Qtrocious/AuraCTRL/PCB/Radiant.kicad_sch

## KiCad design PCB/Radiant.kicad_sch (2025-06-26)

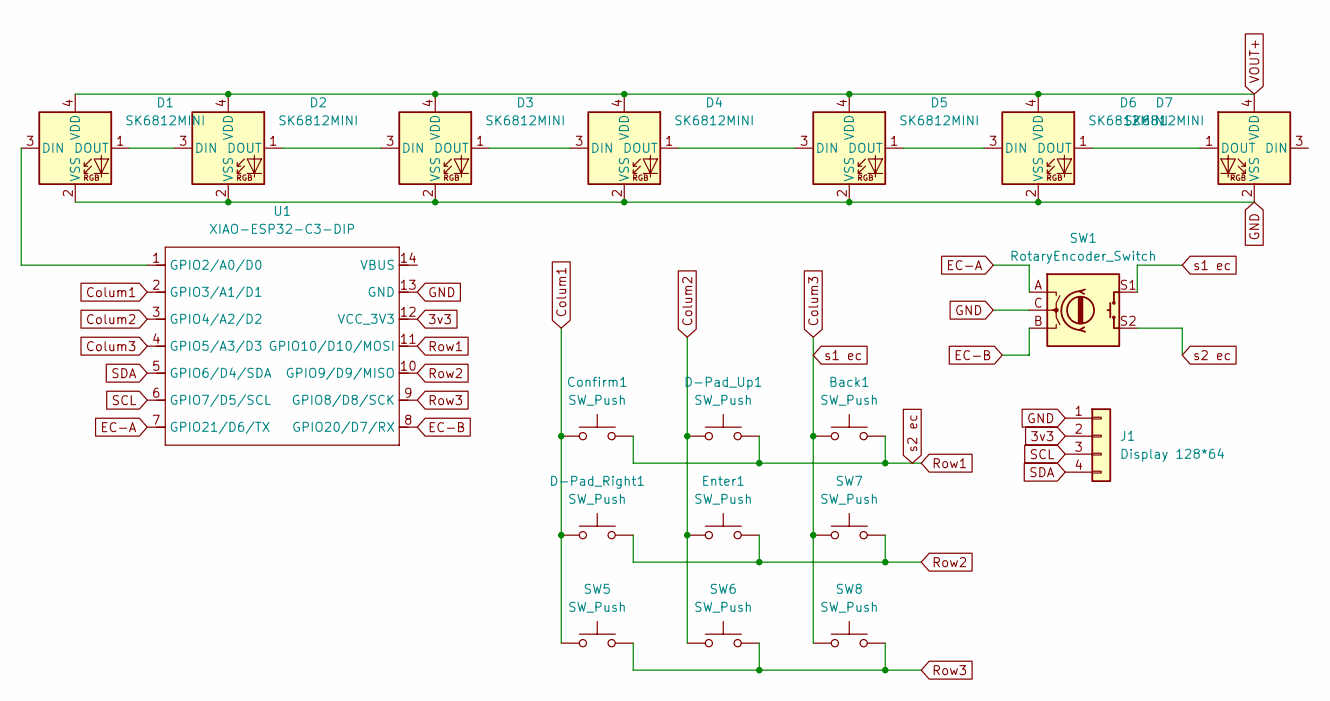
[picture p13: schematic Radiant.kicad_sch]

Parts:
Back1: SW_Push; SW_PUSH_6mm
Confirm1: SW_Push; SW_PUSH_6mm
D1, D2, D3, D4, D5, D6, D7: SK6812MINI; SK6812-MINI-E
D-Pad_Right1: SW_Push; SW_PUSH_6mm
D-Pad_Up1: SW_Push; SW_PUSH_6mm
Enter1: SW_Push; SW_PUSH_6mm
J1: Display 128*64; 128x64OLED
SW1: RotaryEncoder_Switch; RotaryEncoder_Alps_EC11E-Switch_Vertical_H20mm
SW5, SW6, SW7, SW8: SW_Push; SW_PUSH_6mm
U1: XIAO-ESP32-C3-DIP; XIAO-ESP32C3-DIP

Connections:
3v3: J1.2, U1.12 (VCC_3V3)
Colum1: Confirm1.1, D-Pad_Right1.1, SW5.1, U1.2 (GPIO3/A1/D1)
Colum2: D-Pad_Up1.1, Enter1.1, SW6.1, U1.3 (GPIO4/A2/D2)
Colum3: Back1.1, SW1.S1, SW7.1, SW8.1, U1.4 (GPIO5/A3/D3)
EC-A: SW1.A, U1.7 (GPIO21/D6/TX)
EC-B: SW1.B, U1.8 (GPIO20/D7/RX)
GND: D1.2 (VSS), D2.2 (VSS), D3.2 (VSS), D4.2 (VSS), D5.2 (VSS), D6.2 (VSS), D7.2 (VSS), J1.1, SW1.C, U1.13 (GND)
unnamed: D1.1 (DOUT), D2.3 (DIN)
unnamed: D1.3 (DIN), U1.1 (GPIO2/A0/D0)
unnamed: D2.1 (DOUT), D3.3 (DIN)
unnamed: D3.1 (DOUT), D4.3 (DIN)
unnamed: D4.1 (DOUT), D5.3 (DIN)
unnamed: D5.1 (DOUT), D6.3 (DIN)
unnamed: D6.1 (DOUT), D7.1 (DOUT)
Row1: Back1.2, Confirm1.2, D-Pad_Up1.2, SW1.S2, U1.11 (GPIO10/D10/MOSI)
Row2: D-Pad_Right1.2, Enter1.2, SW7.2, U1.10 (GPIO9/D9/MISO)
Row3: SW5.2, SW6.2, SW8.2, U1.9 (GPIO8/D8/SCK)
SCL: J1.3, U1.6 (GPIO7/D5/SCL)
SDA: J1.4, U1.5 (GPIO6/D4/SDA)
VOUT+: D1.4 (VDD), D2.4 (VDD), D3.4 (VDD), D4.4 (VDD), D5.4 (VDD), D6.4 (VDD), D7.4 (VDD)
